asinghani/craft18/3d_cad/lever.stl

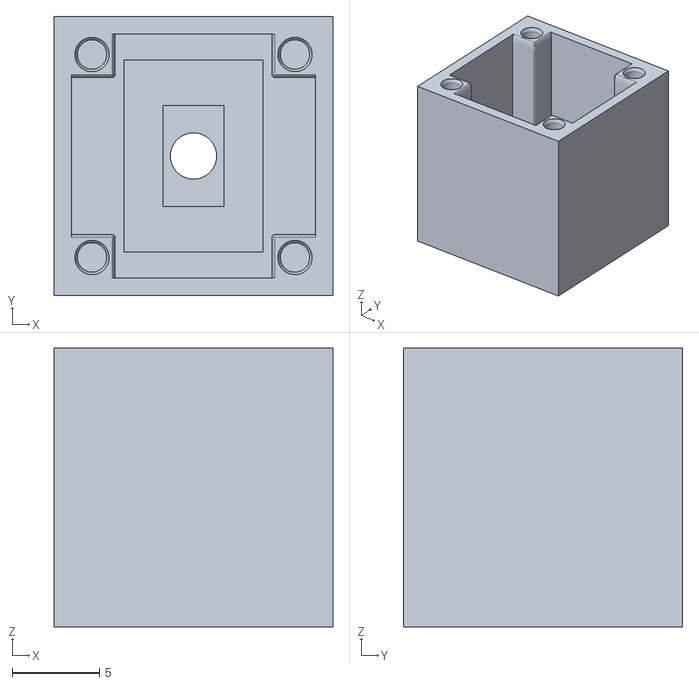
[picture p24: CAD file, 2024-01-21]
3d_cad/lever.stl
16.0 x 16.0 x 16.0
