asinghani/craft18/3d_cad/daylight_sensor_frame.stl

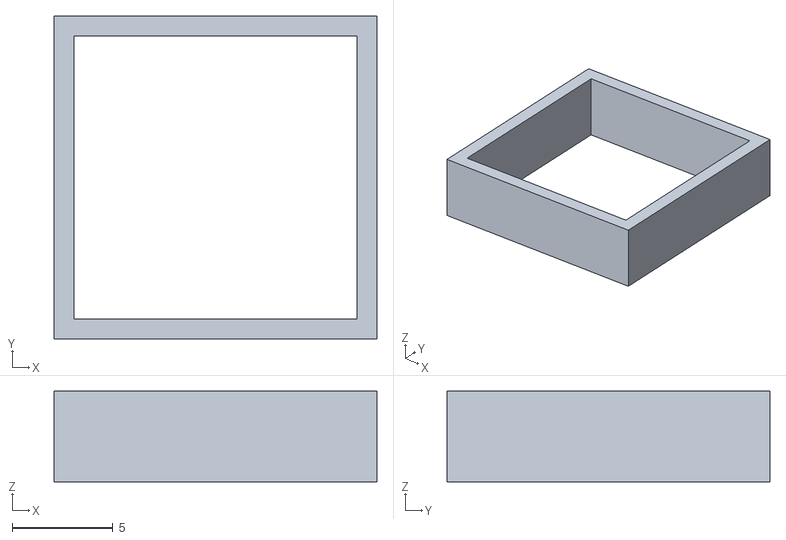
[picture p25: CAD file, 2024-01-21]
3d_cad/daylight_sensor_frame.stl
16.0 x 16.0 x 4.50
