asinghani/craft18/3d_cad/torch_light.stl

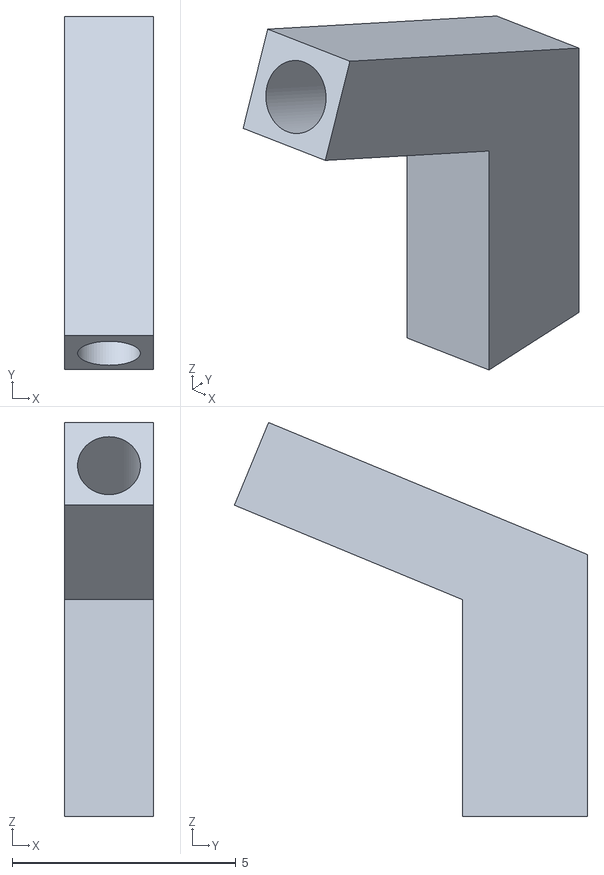
[picture p26: CAD file, 2024-01-21]
3d_cad/torch_light.stl
2.00 x 7.90 x 8.81
