asinghani/craft18/3d_cad/button_top_prescaled.stl

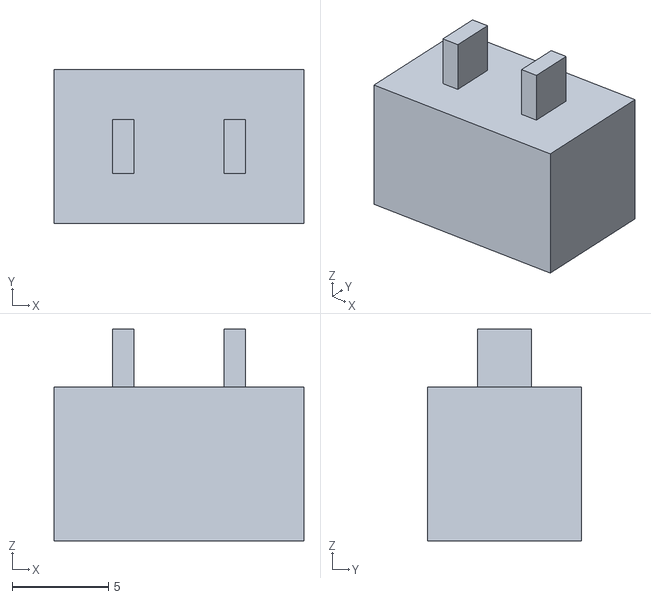
[picture p27: CAD file, 2024-01-21]
3d_cad/button_top_prescaled.stl
13.0 x 8.00 x 11.0
